dheera/aqi-monitor/code/config.py

LOAD_UPLOAD = True     # streams data to a self-hosted server (see server/); requires credentials.json with url, device_id, api_key
LOAD_WATCHDOG = True   # initiates a watchdog so the uc resets if any blocking call hangs for more than 30 seconds
LOAD_DISPLAY = True    # 128x32 OLED display: https://www.adafruit.com/product/4440
LOAD_BME680 = True     # pressure, humidity, temperature, voc: https://www.adafruit.com/product/3660
LOAD_SGP30 = True      # voc (better than bme680): https://www.adafruit.com/product/3709
LOAD_SCD30 = True      # co2, humidity, temp: https://www.seeedstudio.com/Grove-CO2-Temperature-Humidity-Sensor-SCD30-p-2911.html
LOAD_MCGASV2 = True    # multi-channel gas sensor: https://www.seeedstudio.com/Grove-Multichannel-Gas-Sensor-v2-p-4569.html
LOAD_SEN0321 = True    # ozone sensor: https://www.dfrobot.com/product-2005.html
LOAD_BNO08X = True    # imu: https://www.adafruit.com/product/4754
LOAD_PMSA003I = True   # air quality particulate matter sensor: https://www.adafruit.com/product/4632
LOAD_RADSENSE = True   # RadSense 1.2 Geiger counter https://www.ebay.com/itm/Arduino-dosimeter-module-Geiger-Counter-RadSens-Radiation-Detector-board-pcb-/184495660379

# Self-heating offsets (degrees C, subtracted from the raw reading). 0.0 = no
# correction.
BME680_TEMP_OFFSET = 0.0
SCD30_TEMP_OFFSET = 0.0
